X-death25/MD-Dumper_old_stm32F4/docs/Sega Cartridges/04.gif

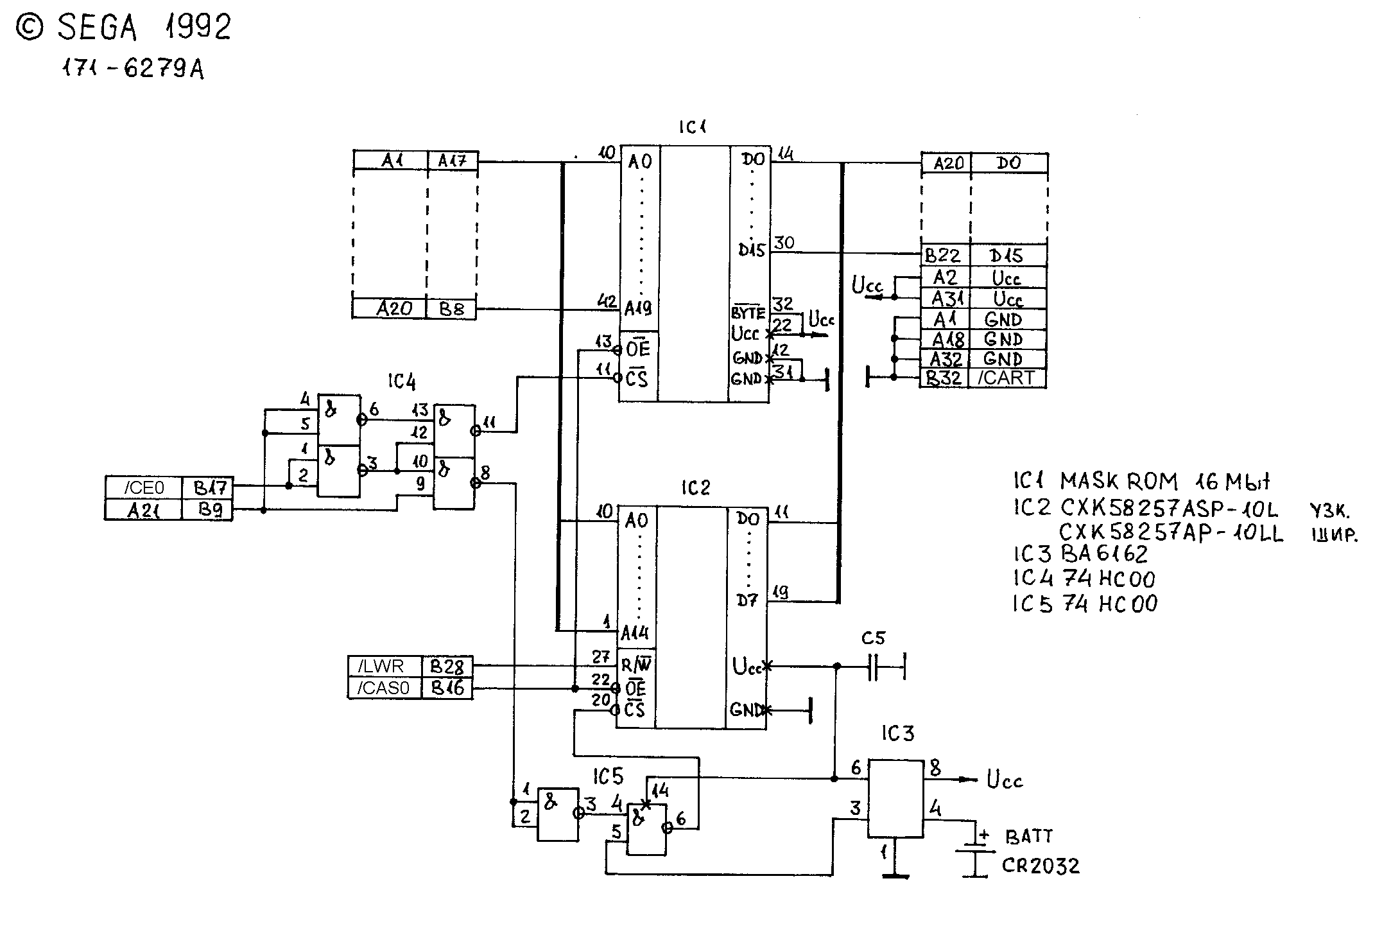
docs/Sega Cartridges/04.gif
